borkdlabs/hoppy_clock/firmware/Core/Inc/w25q128jv_hal_qspi.h

/*******************************************************************************
 * @file w25q128jv_hal_qspi.h
 * @brief W25Q128JV functions: abstracting STM32 HAL: QUADSPI.
 *******************************************************************************
 * @note:
 * Read/write/erase are non-blocking (DMA + QUADSPI IRQ), poll w25q_get_state()
 * for completion. Init/read_id are blocking init-time probes. Transfers use the
 * quad lines (0xEB read, 0x32 program), quad mode is enabled at init.
 *
 * w25q_mmap_enable() exposes the flash read-only at W25Q_MMAP_BASE for direct
 * pointer access, mutually exclusive with the indirect ops (which return
 * HAL_ERROR while mapped). The caller decides when to switch.
 *******************************************************************************
 */

#ifndef HOPPY_CLOCK__W25Q128JV_HAL_QSPI_H
#define HOPPY_CLOCK__W25Q128JV_HAL_QSPI_H

/** Includes. *****************************************************************/

#include "stm32l4xx_hal.h"
#include <stdbool.h>

/** STM32 port and pin configs. ***********************************************/

extern QSPI_HandleTypeDef hqspi;

// QUADSPI.
#define W25Q_HQSPI hqspi

/** Definitions. **************************************************************/

// Expected JEDEC ID (0x9F) bytes for the W25Q128JV.
#define W25Q_MANUFACTURER_ID 0xEF // Winbond.
#define W25Q_MEMORY_TYPE 0x40
#define W25Q_CAPACITY 0x18 // 128 Mbit.

// Memory geometry.
#define W25Q_PAGE_SIZE 256U    // Bytes per programmable page.
#define W25Q_SECTOR_SIZE 4096U // Bytes per erasable sector.
#define W25Q_BLOCK_SIZE 65536U // Bytes per erasable 64 KB block.

// Maximum bytes moved by a single w25q_read(): the DMA transfer counter (CNDTR)
// is 16-bit, so one transfer is capped at 65535 bytes.
#define W25Q_READ_MAX 65535U

// QUADSPI memory-mapped window. Once w25q_mmap_enable() is active, flash byte N
// is readable directly at (const uint8_t *)(W25Q_MMAP_BASE + N).
#define W25Q_MMAP_BASE QSPI_BASE
#define W25Q_MMAP_PTR(addr) ((const void *)(W25Q_MMAP_BASE + (uint32_t)(addr)))

// Instruction set. Reads/writes use the quad-line variants; the remainder are
// single-line.
#define W25Q_CMD_WRITE_ENABLE 0x06
#define W25Q_CMD_READ_STATUS_1 0x05
#define W25Q_CMD_READ_STATUS_2 0x35
#define W25Q_CMD_WRITE_STATUS_2 0x31
#define W25Q_CMD_READ_JEDEC_ID 0x9F
#define W25Q_CMD_FAST_READ_QUAD_IO 0xEB
#define W25Q_CMD_QUAD_PAGE_PROGRAM 0x32
#define W25Q_CMD_SECTOR_ERASE 0x20
#define W25Q_CMD_BLOCK_ERASE_64K 0xD8

// Quad I/O Fast Read (0xEB): 8 mode bits (M7-M0) then 4 dummy clocks follow the
// address. Mode bits of 0x00 keep continuous-read mode disabled so every read
// re-sends the instruction.
#define W25Q_QUAD_READ_MODE_BITS 0x00
#define W25Q_QUAD_READ_DUMMY_CYCLES 4

// Status register bits.
#define W25Q_SR1_BUSY 0x01 // SR-1: write or erase in progress.
#define W25Q_SR2_QE 0x02   // SR-2: Quad Enable.

// Timeout (ms) for the short, blocking command-setup phase of each operation,
// and for the blocking Status Register-2 write during quad-mode enable.
#define W25Q_CMD_TIMEOUT_MS 100U
#define W25Q_STATUS_WRITE_TIMEOUT_MS 100U

/** Public types. *************************************************************/

/**
 * @brief Driver operation state, reported by w25q_get_state().
 */
typedef enum {
  W25Q_STATE_IDLE = 0, // Ready to accept a new operation.
  W25Q_STATE_BUSY,     // An operation is in progress.
  W25Q_STATE_ERROR,    // The last operation failed.
} w25q_state_t;

/** Public functions. *********************************************************/

/**
 * @brief Initialize, probe and enable quad mode on the W25Q128JV.
 *
 * Reads the JEDEC ID (blocking), checks it against the expected W25Q128JV
 * signature, then sets the Status Register-2 QE bit if not already set so quad
 * read/program work. Must be called once, after the QUADSPI peripheral is
 * initialized (MX_QUADSPI_Init) and while no asynchronous operation is in
 * flight.
 *
 * @return HAL_OK on success, HAL_ERROR on a signature mismatch, HAL error
 * status otherwise.
 */
HAL_StatusTypeDef w25q_init(void);

/**
 * @brief Read the 3-byte JEDEC ID (0x9F) (blocking, single-line).
 *
 * @param id Destination for the 3 ID bytes: [0] manufacturer, [1] memory type,
 * [2] capacity.
 *
 * @return HAL_OK on success, HAL error status otherwise.
 */
HAL_StatusTypeDef w25q_read_id(uint8_t id[3]);

/**
 * @brief Launch a non-blocking Quad I/O Fast Read (0xEB) into a buffer via DMA.
 *
 * Returns as soon as the transfer is started; the read is complete once
 * w25q_get_state() returns W25Q_STATE_IDLE. The destination buffer must stay
 * valid until then. Requires quad mode (enabled by w25q_init()).
 *
 * @param address Byte address to start reading from (0 .. 16 MB - 1).
 * @param buffer Destination buffer (must persist until completion).
 * @param length Number of bytes to read (1 .. W25Q_READ_MAX).
 *
 * @return HAL_OK if the read was launched, HAL_BUSY if another operation is in
 * flight, HAL error status otherwise.
 */
HAL_StatusTypeDef w25q_read(uint32_t address, uint8_t *buffer, uint32_t length);

/**
 * @brief Launch a non-blocking write of arbitrary length via DMA.
 *
 * Splits the write across 256-byte pages automatically, issuing Write Enable
 * and Quad Input Page Program (0x32) per page and chaining pages from the
 * QUADSPI interrupt. Returns as soon as the first page is started, the write is
 * complete once w25q_get_state() returns W25Q_STATE_IDLE. The source buffer
 * must stay valid until then, the target range must have been erased (0xFF)
 * beforehand, and quad mode must be enabled (by w25q_init()).
 *
 * @param address Byte address to start programming at.
 * @param buffer Source bytes (must persist until completion).
 * @param length Number of bytes to program.
 *
 * @return HAL_OK if the write was launched, HAL_BUSY if another operation is in
 * flight, HAL error status otherwise.
 */
HAL_StatusTypeDef w25q_write(uint32_t address, const uint8_t *buffer,
                             uint32_t length);

/**
 * @brief Launch a non-blocking erase of the 4 KB sector at an address.
 *
 * Issues Write Enable then Sector Erase (0x20, single-line) and waits for
 * completion on the QUADSPI interrupt. The whole 4 KB sector is set to 0xFF.
 * The erase is complete once w25q_get_state() returns W25Q_STATE_IDLE.
 *
 * @param address Any byte address within the sector to erase.
 *
 * @return HAL_OK if the erase was launched, HAL_BUSY if another operation is in
 * flight, HAL error status otherwise.
 */
HAL_StatusTypeDef w25q_erase_sector(uint32_t address);

/**
 * @brief Launch an erase of the 64 KB block at an address (blocking-on-IRQ).
 *
 * Issues Write Enable then Block Erase (0xD8, single-line) and waits for
 * completion on the QUADSPI interrupt. The whole 64 KB block is set to 0xFF --
 * ~16x fewer commands than sector-erasing the same span. Complete once
 * w25q_get_state() returns W25Q_STATE_IDLE.
 *
 * @param address Any byte address within the 64 KB block to erase.
 *
 * @return HAL_OK if the erase was launched, HAL_BUSY if another operation is in
 * flight, HAL error status otherwise.
 */
HAL_StatusTypeDef w25q_erase_block_64k(uint32_t address);

/**
 * @brief Get the current driver state.
 *
 * @return W25Q_STATE_IDLE when ready, W25Q_STATE_BUSY while an operation is in
 * flight, W25Q_STATE_ERROR if the last operation failed.
 */
w25q_state_t w25q_get_state(void);

/**
 * @brief Enter memory-mapped mode: flash becomes readable at W25Q_MMAP_BASE.
 *
 * Configures the Quad I/O Fast Read (0xEB) recipe as a memory-mapped read so
 * any CPU/DMA access to W25Q_MMAP_BASE + offset returns flash data directly. No
 * indirect read/write/erase may be issued while mapped. Requires quad mode
 * (w25q_init()). Idempotent.
 *
 * @return HAL_OK on success (or already mapped), HAL_BUSY if an indirect
 * operation is in flight, HAL error status otherwise.
 */
HAL_StatusTypeDef w25q_mmap_enable(void);

/**
 * @brief Leave memory-mapped mode and return the peripheral to indirect mode.
 *
 * Aborts the memory-mapped decode so w25q_read()/w25q_write()/w25q_erase_sector()
 * can be used again. Call this before programming. Idempotent.
 *
 * @return HAL_OK on success (or already indirect), HAL error status otherwise.
 */
HAL_StatusTypeDef w25q_mmap_disable(void);

/**
 * @brief Whether the peripheral is currently in memory-mapped mode.
 *
 * @return true if mapped (indirect ops unavailable), false if indirect.
 */
bool w25q_is_memory_mapped(void);

#endif
