borkdlabs/hoppy_clock/firmware/Core/Inc/ws2812b_hal_pwm.h

/**
 *******************************************************************************
 * @file:  ws2812b_hal_pwm.h
 * @brief: WS2812B functions: abstracting STM32 HAL: PWM.
 *******************************************************************************
 * @note:
 * Based on Phil's Lab "STM32 + RGB LEDs Firmware Tutorial (TIM + DMA) - Phil's
 * Lab #136" (https://youtu.be/MqbJTj0Cw6o).
 *******************************************************************************
 */

#ifndef HOPPY_CLOCK__WS2812B_HAL_PWM_H
#define HOPPY_CLOCK__WS2812B_HAL_PWM_H

/** Includes. *****************************************************************/

#include "stm32l4xx_hal.h"

/** STM32 port and pin configs. ***********************************************/

extern TIM_HandleTypeDef htim1;

// PWM timer channel.
#define WS2812B_TIM_INSTANCE TIM1
#define WS2812B_TIM htim1
#define WS2812B_TIM_CHANNEL TIM_CHANNEL_1

/** Definitions. **************************************************************/

// Maximum LEDs the DMA buffer and colour arrays are sized for (compile-time).
// The active count is a runtime value (ws2812b_set_count), 1..LED_COUNT_MAX,
// since a WS2812B chain is write-only and can't be auto-probed.
#define LED_COUNT_MAX 64u
#define LED_COUNT_DEFAULT 1u // Onboard LED only, until configured.

// Based on 80 MHz peripheral clock at 25-1 prescaler and 25-1 ARR with time
// period of 1.25 us. See README.md calculations.
#define WS2812B_LO_VAL_DUTY 8      // 0.4 us.
#define WS2812B_HI_VAL_DUTY 16     // 0.8 us.
#define WS2812B_RST_VAL_PERIODS 40 // 50 us.
#define WS2812B_BITS_PER_LED 24    // (8 * 3 = 24) 1 byte per R, G and B value.

#define WS2812B_DMA_BUF_LEN                                                    \
  ((uint16_t)((LED_COUNT_MAX * WS2812B_BITS_PER_LED) + WS2812B_RST_VAL_PERIODS))

/** Public types. *************************************************************/

/**
 * @brief  Union for representing WS2812B LED color data.
 *
 * This union is designed to store and manipulate the color data for a single
 * WS2812B LED. The color data can be accessed either as individual RGB
 * components (red, green, blue) or as a combined 32-bit value.
 *
 * The structure within the union allows for easy manipulation of the red,
 * green, and blue color channels individually, while the `data` field provides
 * a way to handle the entire 24-bit color value as a single unit.
 *
 * The bit order in the `data` field is:
 * - G7, G6, ..., G0 (Green channel, most to least significant bit).
 * - R7, R6, ..., R0 (Red channel, most to least significant bit).
 * - B7, B6, ..., B0 (Blue channel, most to least significant bit).
 *
 * Usage example:
 * @code
 * WS2812B_LED_DATA_RGB led;
 *
 * // Set individual color components.
 * led.colour.r = 255; // Max red intensity.
 * led.colour.g = 128; // Half green intensity.
 * led.colour.b = 64;  // Quarter blue intensity.
 *
 * // Alternatively, set the entire color using the data field.
 * led.data = 0xFF8040; // RGB color: (255, 128, 64).
 * @endcode
 */
typedef union {
  struct {
    uint8_t g;
    uint8_t r;
    uint8_t b;
  } colour;

  uint32_t data;

} ws2812b_led_data_t;

/** Public variables. *********************************************************/

extern ws2812b_led_data_t led_data[LED_COUNT_MAX]; // Individual LED data.
extern uint16_t dma_buffer[WS2812B_DMA_BUF_LEN];   // Stores duty cycle values.
extern volatile uint8_t dma_complete_flag; // Flag for DMA send complete.

/** Public functions. *********************************************************/

/**
 * @brief  Initializes the WS2812B LED control system.
 *
 * @return HAL_StatusTypeDef: status of initialization.
 */
HAL_StatusTypeDef ws2812b_init(void);

/**
 * @brief Set the active number of LEDs in the chain (1..LED_COUNT_MAX).
 *
 * Only this many LEDs are clocked out by ws2812b_update(). Clamped to the valid
 * range. Persisted config drives this at boot, the value cannot be auto-probed.
 *
 * @param count Active LED count.
 */
void ws2812b_set_count(uint16_t count);

/**
 * @brief Get the active number of LEDs in the chain.
 *
 * @return Active LED count (1..LED_COUNT_MAX).
 */
uint16_t ws2812b_get_count(void);

/**
 * @brief  Sets the color of a specific WS2812B LED.
 *
 * @param index The index of the LED in the array (0-based index).
 * @param r The red component of the color (0-255).
 * @param g The green component of the color (0-255).
 * @param b The blue component of the color (0-255).
 *
 * Example Usage:
 * @code
 * // Set the first LED to bright red.
 * WS2812B_Set_Colour(0, 255, 0, 0);
 *
 * // Set the second LED to green.
 * WS2812B_Set_Colour(1, 0, 255, 0);
 * @endcode
 */
void ws2812b_set_colour(uint8_t index, uint8_t r, uint8_t g, uint8_t b);

/**
 * @brief  Updates the WS2812B LEDs with the latest color data.
 *
 * @return HAL_StatusTypeDef: status of the operation.
 */
HAL_StatusTypeDef ws2812b_update(void);

/**
 * @brief  Callback function to handle the completion of WS2812B data transfer.
 *
 * Example usage within `HAL_TIM_PWM_PulseFinishedCallback()`:
 * @code
 * void HAL_TIM_PWM_PulseFinishedCallback(TIM_HandleTypeDef *htim) {
 *   ws2812b_callback();
 * }
 * @endcode
 */
void ws2812b_callback(void);

#endif
