borkdlabs/hoppy_clock/firmware/Core/Inc/init.h

/*******************************************************************************
 * @file init.h
 * @brief Centralized init logic running in main.c.
 *******************************************************************************
 */

#ifndef HOPPY_CLOCK__INIT_H
#define HOPPY_CLOCK__INIT_H

/** Public functions. *********************************************************/

void hoppy_clock_init(void);

#endif
