borkdlabs/hoppy_clock/firmware/Core/Inc/run.h

/*******************************************************************************
 * @file run.h
 * @brief Centralized main loop run logic running in main.c.
 *******************************************************************************
 */

#ifndef HOPPY_CLOCK__RUN_H
#define HOPPY_CLOCK__RUN_H

/** Includes. *****************************************************************/

#include "scheduler.h"

/** Public functions. *********************************************************/

void hoppy_clock_run(void);

#endif
